picli3/esp_programmer/doc/IMG_1.png

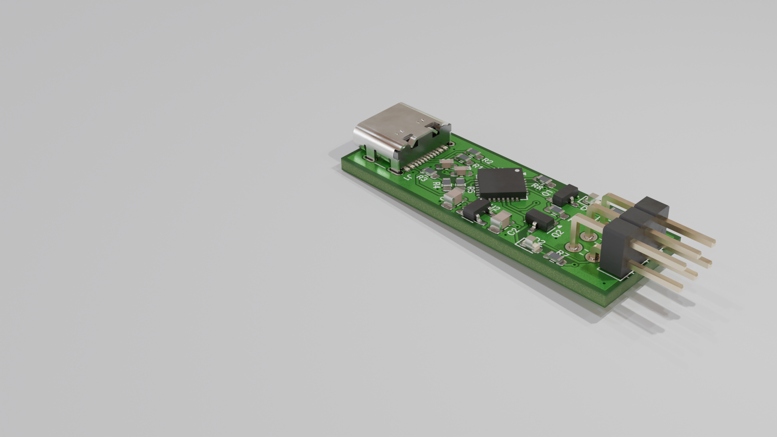
doc/IMG_1.png
