picli3/esp_programmer/doc/IMG_2.png

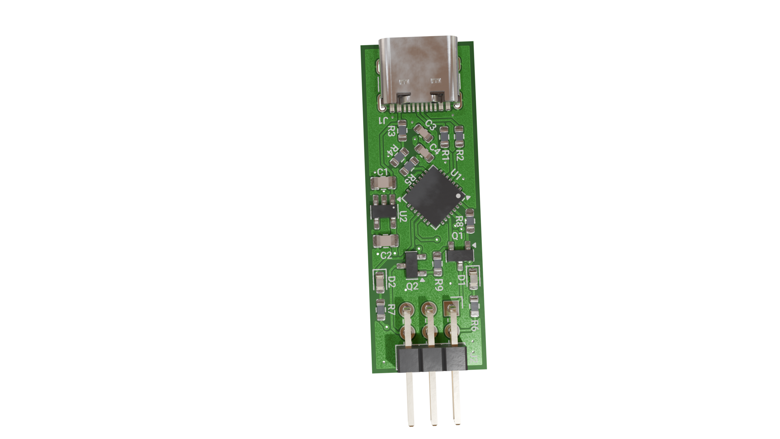
doc/IMG_2.png
